vedranMv/esp32_hotplate/src/screens/base_screen.hpp

#pragma once

#include <ClickEncoder.h>
#include <Adafruit_SSD1306.h>

class BaseScreen
{
public:
    virtual void render(Adafruit_SSD1306 &display) = 0;
    virtual void input_callback(Button::eButtonStates btn_state, int16_t enc_increment) = 0;
};
